Xinyuan-LilyGO/T-Embed/examples/factory/src/knob.png

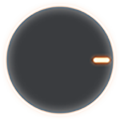
examples/factory/src/knob.png
