Xinyuan-LilyGO/T-Embed/image/front-panel.jpg

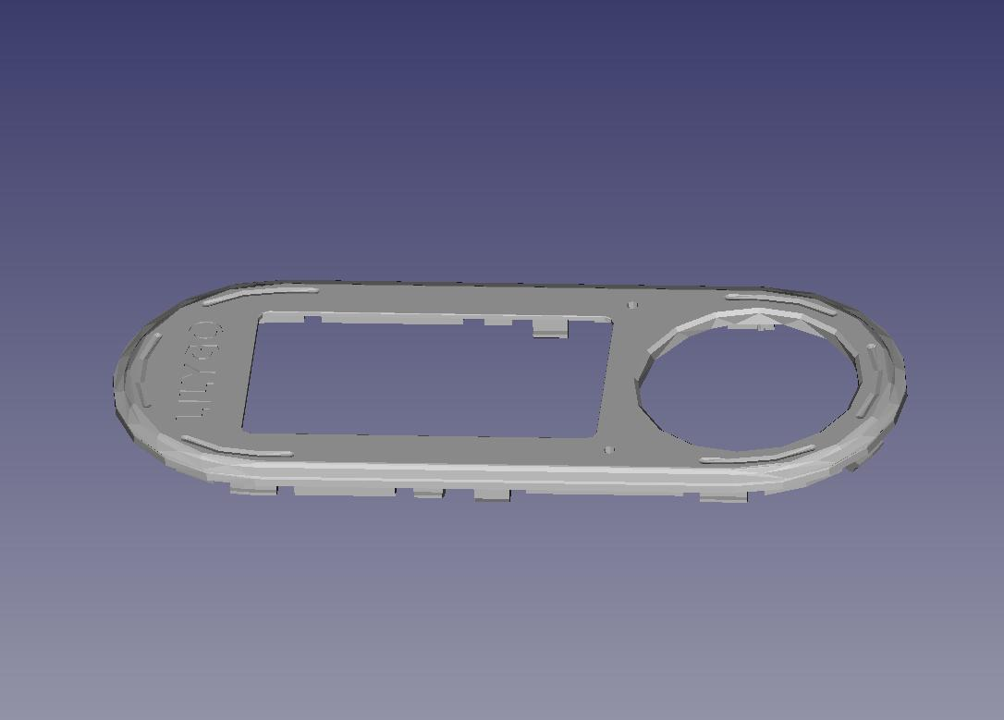
image/front-panel.jpg
