Xinyuan-LilyGO/T-Embed/examples/CC1101_Receive/CC1101_Receive.ino

/**
 * @file      CC1101_Transmit.ino
 * @author    Lewis He (lewishe@outlook.com)
 * @license   MIT
 * @copyright Copyright (c) 2023  Shenzhen Xin Yuan Electronic Technology Co., Ltd
 * @date      2023-10-19
 * @note      The sketch only works with CC1101 + NFC Shield
 */

#include <RadioLib.h>
#include <Adafruit_PN532.h>
#include "TFTHelper.h"
#include "OneButton.h"

static float freq = 0;

enum CC1101_Freq  {
    FREQ_315MHZ,
    FREQ_434MHZ,
    FREQ_868MHZ,
    FREQ_915MHZ,
};

SPIClass newSPI =  SPIClass(HSPI);
CC1101 radio = new Module(SHIELD_RADIO_CS_PIN,
                          SHIELD_RADIO_DIO0_PIN,
                          SHIELD_RADIO_RST_PIN,
                          -1,
                          newSPI);
Adafruit_PN532 nfc(SHIELD_NFC_CS_PIN, &newSPI);

TFT_eSprite spr = TFT_eSprite(&tft);
TFT_eSprite sprTitle = TFT_eSprite(&tft);
TFT_eSprite nfcSpr = TFT_eSprite(&tft);
OneButton button(BOARD_ENCODE_CENTEN_PIN, true);

int spr_w = 0;
int spr_h = 0;
int spr_start_x = 0;
int spr_start_y = 0;
int start_x ;
int title_h ;
SemaphoreHandle_t radioLock;
uint8_t currFreq = FREQ_868MHZ;
bool nfcOnline = true;

void readMifareClassic(void);

void setFreq( CC1101_Freq f)
{
    switch (f) {
    case FREQ_315MHZ:
        digitalWrite(SHIELD_RADIO_SW1_PIN, HIGH);
        digitalWrite(SHIELD_RADIO_SW0_PIN, LOW);
        freq = 315.0;
        return;
    case FREQ_434MHZ:
        digitalWrite(SHIELD_RADIO_SW1_PIN, HIGH);
        digitalWrite(SHIELD_RADIO_SW0_PIN, HIGH);
        freq = 434.0;
        return;
    case FREQ_868MHZ:
        freq = 868.0;
        digitalWrite(SHIELD_RADIO_SW1_PIN, LOW);
        digitalWrite(SHIELD_RADIO_SW0_PIN, HIGH);
        return;
    case FREQ_915MHZ:
        freq = 915.0;
        digitalWrite(SHIELD_RADIO_SW1_PIN, LOW);
        digitalWrite(SHIELD_RADIO_SW0_PIN, HIGH);
        return;
    default:
        break;
    }
    freq = 868.0;
    digitalWrite(SHIELD_RADIO_SW1_PIN, LOW);
    digitalWrite(SHIELD_RADIO_SW0_PIN, HIGH);
}


void clickCallback()
{
    Serial.println("Cilick");
    currFreq++;
    currFreq %= (FREQ_915MHZ + 1);
    setFreq((CC1101_Freq)currFreq);
    if (xSemaphoreTake(radioLock, portMAX_DELAY)) {
        // set carrier frequency
        if (radio.setFrequency(freq) == RADIOLIB_ERR_INVALID_FREQUENCY) {
            Serial.println(F("[CC1101] Selected frequency is invalid for this module!"));
            tft.println(F("[CC1101] Selected frequency is invalid for this module!"));
        } else {
            Serial.println(F("[CC1101] Selected frequency successed!"));
        }

        String str = String(freq);
        str.concat("MHz");

        sprTitle.setFreeFont(&FreeMono9pt7b);
        sprTitle.drawString("Recvive:", 15, 5);
        sprTitle.drawString(str, 15, 25);
        sprTitle.pushSprite(0, 0);

        xSemaphoreGive(radioLock);
    }
}


void buttonLoop(void *)
{
    while (1) {
        button.tick();
        delay(5);
    }
}

void setup()
{
    Serial.begin(115200);

    // Create lock
    radioLock = xSemaphoreCreateBinary();
    xSemaphoreGive(radioLock);

    // Using battery requires setting IO46 to HIGH,
    // otherwise the device will not allow
    pinMode(BOARD_POWER_ON_PIN, OUTPUT);
    digitalWrite(BOARD_POWER_ON_PIN, HIGH);

    // Initialize display screen
    initTFT();

    spr_w = tft.width();
    spr_h = tft.width() / 3;

    // Radio and NFC ,SD share the SPI bus.
    // Before using it, turn off and disable all devices
    // on the same bus.
    pinMode(SHIELD_RADIO_CS_PIN, OUTPUT);
    digitalWrite(SHIELD_RADIO_CS_PIN, HIGH);

    pinMode(SHIELD_NFC_CS_PIN, OUTPUT);
    digitalWrite(SHIELD_NFC_CS_PIN, HIGH);

    pinMode(BOARD_SDCARD_CS_PIN, OUTPUT);
    digitalWrite(BOARD_SDCARD_CS_PIN, HIGH);

    //Set antenna frequency settings
    pinMode(SHIELD_RADIO_SW1_PIN, OUTPUT);
    pinMode(SHIELD_RADIO_SW0_PIN, OUTPUT);
    //Set CC1101 frequency
    setFreq(FREQ_868MHZ);

    // Initialize SPI
    newSPI.begin(BOARD_SPI_SCK_PIN, BOARD_SPI_MISO_PIN, BOARD_SPI_MOSI_PIN);


    nfc.begin();
    uint32_t versiondata = nfc.getFirmwareVersion();
    if (! versiondata) {
        Serial.println("Didn't find PN53x chip");
        tft.println("Didn't find PN53x chip");
        delay(1000);
        nfcOnline = false;
    } else {
        // Got ok data, print it out!
        Serial.print("Found chip PN5"); Serial.println((versiondata >> 24) & 0xFF, HEX);
        Serial.print("Firmware ver. "); Serial.print((versiondata >> 16) & 0xFF, DEC);
        Serial.print('.'); Serial.println((versiondata >> 8) & 0xFF, DEC);
        Serial.println("Waiting for an ISO14443A Card ...");
    }


    // initialize CC1101
    Serial.print(F("[CC1101] Initializing ... "));
    Serial.print(freq);
    Serial.print(" MHz ");

    tft.print(F("[CC1101] Initializing ... "));
    tft.print(freq);
    tft.print(" MHz ");

    int state = radio.begin(freq);
    if (state == RADIOLIB_ERR_NONE) {
        Serial.println(F("success!"));
        tft.println(F("success!"));
    } else {
        Serial.print(F("failed, code "));
        Serial.println(state);
        tft.print(F("failed, code "));
        tft.println(state);
        while (true);
    }


    // you can also change the settings at runtime
    // and check if the configuration was changed successfully

    // set carrier frequency to 433.5 MHz
    if (radio.setFrequency(freq) == RADIOLIB_ERR_INVALID_FREQUENCY) {
        Serial.println(F("[CC1101] Selected frequency is invalid for this module!"));
        tft.println(F("[CC1101] Selected frequency is invalid for this module!"));
        while (true);
    }

    // Too high an air rate may result in data loss
    // Set bit rate to 5 kbps
    state = radio.setBitRate(5);
    if (state == RADIOLIB_ERR_INVALID_BIT_RATE) {
        Serial.println(F("[CC1101] Selected bit rate is invalid for this module!"));
        tft.println(F("[CC1101] Selected bit rate is invalid for this module!"));
        while (true);
    } else if (state == RADIOLIB_ERR_INVALID_BIT_RATE_BW_RATIO) {
        Serial.println(F("[CC1101] Selected bit rate to bandwidth ratio is invalid!"));
        Serial.println(F("[CC1101] Increase receiver bandwidth to set this bit rate."));
        tft.println(F("[CC1101] Increase receiver bandwidth to set this bit rate."));
        while (true);
    }

    // set receiver bandwidth to 135.0 kHz
    if (radio.setRxBandwidth(135.0) == RADIOLIB_ERR_INVALID_RX_BANDWIDTH) {
        Serial.println(F("[CC1101] Selected receiver bandwidth is invalid for this module!"));
        tft.println(F("[CC1101] Selected receiver bandwidth is invalid for this module!"));
        while (true);
    }

    // set allowed frequency deviation to 10.0 kHz
    if (radio.setFrequencyDeviation(10.0) == RADIOLIB_ERR_INVALID_FREQUENCY_DEVIATION) {
        Serial.println(F("[CC1101] Selected frequency deviation is invalid for this module!"));
        tft.println(F("[CC1101] Selected frequency deviation is invalid for this module!"));
        while (true);
    }

    // set output power to 10 dBm
    if (radio.setOutputPower(10) == RADIOLIB_ERR_INVALID_OUTPUT_POWER) {
        Serial.println(F("[CC1101] Selected output power is invalid for this module!"));
        tft.println(F("[CC1101] Selected output power is invalid for this module!"));
        while (true);
    }

    // 2 bytes can be set as sync word
    if (radio.setSyncWord(0x01, 0x23) == RADIOLIB_ERR_INVALID_SYNC_WORD) {
        Serial.println(F("[CC1101] Selected sync word is invalid for this module!"));
        tft.println(F("[CC1101] Selected sync word is invalid for this module!"));
        while (true);
    }

    start_x = (tft.width() / 2) - 2;
    title_h = tft.height() - spr_h - 10;

    sprTitle.createSprite(tft.width() / 2, title_h);
    sprTitle.fillSprite(TFT_BLACK);
    sprTitle.drawRoundRect(0, 0, start_x, title_h, 5, TFT_VIOLET);

    String str = String(freq);
    str.concat("MHz");

    sprTitle.setFreeFont(&FreeMono9pt7b);
    sprTitle.drawString("Recvive:", 15, 5);
    sprTitle.drawString(str, 15, 25);

    sprTitle.pushSprite(0, 0);


    nfcSpr.createSprite(tft.width() / 2, title_h);
    nfcSpr.fillSprite(TFT_BLACK);
    nfcSpr.setFreeFont(&FreeMono9pt7b);
    nfcSpr.drawRoundRect(0, 0, start_x, title_h, 5, TFT_DARKCYAN);
    str = "NFC";
    nfcSpr.drawString(str,  15, 5);
    if (!nfcOnline) {
        nfcSpr.setTextFont(1);
        nfcSpr.setTextColor(TFT_RED);
        str = "FAIL";
        nfcSpr.drawString(str, 15, 25);
    }
    nfcSpr.pushSprite(start_x, 0);


    spr_start_x = 10;
    spr_start_y = 35;
    spr.createSprite(spr_w, spr_h);
    spr.fillSprite(TFT_BLACK);
    spr.drawRoundRect(0, 0, spr_w - 2, spr_h - 2, 5, TFT_ORANGE);
    spr.setCursor(spr_start_x, spr_start_y);
    spr.setFreeFont(&FreeSerif9pt7b);
    spr.println(F("Waiting for incoming transmission ... "));
    spr.pushSprite(0, tft.height() / 3);


    button.attachClick(clickCallback);

    xTaskCreate(buttonLoop, "btn", 2048, NULL, 10, NULL);
}


void loop()
{
    if (nfcOnline) {
        // Block for 2 seconds to read the tag
        readMifareClassic();
    }

    if (xSemaphoreTake(radioLock, pdMS_TO_TICKS(200)) != pdPASS) {
        return;
    }

    Serial.print(F("[CC1101] Waiting for incoming transmission ... "));

    // you can receive data as an Arduino String
    String str;
    int state = radio.receive(str);

    // you can also receive data as byte array
    /*
      byte byteArr[8];
      int state = radio.receive(byteArr, 8);
    */

    if (state == RADIOLIB_ERR_NONE) {

        // Add data filtering to only match the corresponding character prefix.
        // If you do not add a data prefix, it may be interfered by other products with the same frequency.
        if (!str.startsWith("Embed:")) {
            xSemaphoreGive(radioLock);
            return;
        }
        // remove prefix
        str = str.substring(String("Embed:").length());

        // packet was successfully received
        Serial.println(F("success!"));

        // print the data of the packet
        Serial.print(F("[CC1101] Data:\t\t"));
        Serial.println(str);

        // print RSSI (Received Signal Strength Indicator)
        // of the last received packet
        Serial.print(F("[CC1101] RSSI:\t\t"));
        Serial.print(radio.getRSSI());
        Serial.println(F(" dBm"));

        // print LQI (Link Quality Indicator)
        // of the last received packet, lower is better
        Serial.print(F("[CC1101] LQI:\t\t"));
        Serial.println(radio.getLQI());

        spr.fillSprite(TFT_BLACK);
        spr.drawRoundRect(0, 0, spr_w - 2, spr_h - 2, 5, TFT_ORANGE);
        spr.setCursor(spr_start_x, spr_start_y);
        spr.print(F("Data:"));
        spr.println(str);
        // spr.setCursor(spr_start_x, spr_start_y + 15);
        spr.print(F(" \n  RSSI:"));
        spr.print(radio.getRSSI());
        spr.println(F(" dBm"));
        spr.pushSprite(0, tft.height() / 3);

    } else if (state == RADIOLIB_ERR_RX_TIMEOUT) {
        // timeout occurred while waiting for a packet
        Serial.println(F("timeout!"));

    } else if (state == RADIOLIB_ERR_CRC_MISMATCH) {
        // packet was received, but is malformed
        Serial.println(F("CRC error!"));

    } else {
        // some other error occurred
        Serial.print(F("failed, code "));
        Serial.println(state);
    }

    xSemaphoreGive(radioLock);

}

void readMifareClassic(void)
{
    uint8_t success;
    uint8_t uid[] = { 0, 0, 0, 0, 0, 0, 0 };  // Buffer to store the returned UID
    uint8_t uidLength;                        // Length of the UID (4 or 7 bytes depending on ISO14443A card type)

    // Wait for an ISO14443A type cards (Mifare, etc.).  When one is found
    // 'uid' will be populated with the UID, and uidLength will indicate
    // if the uid is 4 bytes (Mifare Classic) or 7 bytes (Mifare Ultralight)
    success = nfc.readPassiveTargetID(PN532_MIFARE_ISO14443A, uid, &uidLength, 2000);
    Serial.print("readPassiveTargetID:");
    Serial.println(success);
    if (success) {
        // Display some basic information about the card
        Serial.println("Found an ISO14443A card");
        Serial.print("  UID Length: "); Serial.print(uidLength, DEC); Serial.println(" bytes");
        Serial.print("  UID Value: ");
        nfc.PrintHex(uid, uidLength);


        //Show uid
        nfcSpr.fillSprite(TFT_BLACK);
        nfcSpr.drawRoundRect( 2, 0, start_x, title_h, 5, TFT_DARKCYAN);
        nfcSpr.setFreeFont(&FreeMono9pt7b);

        String str = "NFC";
        nfcSpr.drawString(str,  15, 5);
        nfcSpr.setTextFont(1);
        str = "UID:";
        str.concat(uid[0]); str.concat(':');
        str.concat(uid[1]); str.concat(':');
        str.concat(uid[2]); str.concat(':');
        str.concat(uid[3]);
        nfcSpr.drawString(str, 15, 25);

        nfcSpr.pushSprite(start_x, 0);

        if (uidLength == 4) {
            // We probably have a Mifare Classic card ...
            uint32_t cardid = uid[0];
            cardid <<= 8;
            cardid |= uid[1];
            cardid <<= 8;
            cardid |= uid[2];
            cardid <<= 8;
            cardid |= uid[3];
            Serial.print("Seems to be a Mifare Classic card #");
            Serial.println(cardid);
        }
        Serial.println("");
    } else {
        nfcSpr.fillSprite(TFT_BLACK);
        String str = "NFC";
        nfcSpr.setFreeFont(&FreeMono9pt7b);
        nfcSpr.drawRoundRect( 2, 0, start_x, title_h, 5, TFT_DARKCYAN);
        nfcSpr.drawString(str,  15, 5);
        nfcSpr.pushSprite(start_x, 0);
    }
}
