Xinyuan-LilyGO/T-Embed/examples/factory/src/img_controller.c

#if defined(LV_CONF_INCLUDE_SIMPLE)
#include "lvgl.h"
#else
 #include "lvgl.h"
#endif


#ifndef LV_ATTRIBUTE_MEM_ALIGN
#define LV_ATTRIBUTE_MEM_ALIGN
#endif

#ifndef LV_ATTRIBUTE_IMG_IMG_CONTROLLER
#define LV_ATTRIBUTE_IMG_IMG_CONTROLLER
#endif

const LV_ATTRIBUTE_MEM_ALIGN LV_ATTRIBUTE_LARGE_CONST LV_ATTRIBUTE_IMG_IMG_CONTROLLER uint8_t img_controller_map[] = {
#if LV_COLOR_DEPTH == 1 || LV_COLOR_DEPTH == 8
  /*Pixel format: Alpha 8 bit, Red: 3 bit, Green: 3 bit, Blue: 2 bit*/
  0x00, 0x00, 0x00, 0x00, 0x00, 0x00, 0x00, 0x00, 0x00, 0x00, 0x00, 0x00, 0x00, 0x00, 0x00, 0x8d, 0x00, 0xe8, 0x00, 0xf2, 0x00, 0xf2, 0x00, 0xf2, 0x00, 0xf2, 0x00, 0xf2, 0x00, 0xf2, 0x00, 0xf2, 0x00, 0xf2, 0x00, 0xf2, 0x00, 0xf2, 0x00, 0xc1, 0x00, 0x29, 0x00, 0x00, 0x00, 0x00, 0x00, 0x00, 0x00, 0x00, 0x00, 0x00, 0x00, 0x00, 0x00, 0x00, 0x00, 0x00, 0x00, 0x00, 0x00, 0x00, 0x00, 0x00, 0x00, 0x00, 0x00, 0x51, 0x00, 0xd3, 0x00, 0xf2, 0x00, 0xf2, 0x00, 0xf2, 0x00, 0xf2, 0x00, 0xf2, 0x00, 0xf2, 0x00, 0xf2, 0x00, 0xf2, 0x00, 0xf2, 0x00, 0xf2, 0x00, 0xde, 0x00, 0x69, 0x00, 0x00, 0x00, 0x00, 0x00, 0x00, 0x00, 0x00, 0x00, 0x00, 0x00, 0x00, 0x00, 0x00, 0x00, 0x00, 0x00, 0x00, 0x00, 0x00, 0x00, 0x00, 0x00, 0x00, 0x00, 0x17, 0x00, 0xb5, 0x00, 0xf2, 0x00, 0xf2, 0x00, 0xf2, 0x00, 0xf2, 0x00, 0xf2, 0x00, 0xf2, 0x00, 0xf2, 0x00, 0xf2, 0x00, 0xf2, 0x00, 0xf2, 0x00, 0xee, 0x00, 0x9f, 0x00, 0x09, 0x00, 0x00, 0x00, 0x00, 0x00, 0x00, 0x00, 0x00, 0x00, 0x00, 0x00, 0x00, 
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
