Xinyuan-LilyGO/T-Embed/examples/factory/src/alibaba_font.c

/*******************************************************************************
 * Size: 40 px
 * Bpp: 4
 * Opts: 
 ******************************************************************************/

#ifdef LV_CONF_INCLUDE_SIMPLE
#include "lvgl.h"
#else
 #include "lvgl.h"
#endif

#ifndef ALIBABA_FONT
#define ALIBABA_FONT 1
#endif

#if ALIBABA_FONT

/*-----------------
 *    BITMAPS
 *----------------*/

/*Store the image of the glyphs*/
static LV_ATTRIBUTE_LARGE_CONST const uint8_t glyph_bitmap[] = {
    /* U+0020 " " */

    /* U+0021 "!" */
    0x7f, 0xff, 0xff, 0xff, 0xc6, 0xff, 0xff, 0xff,
    0xfb, 0x6f, 0xff, 0xff, 0xff, 0xa5, 0xff, 0xff,
    0xff, 0xf9, 0x4f, 0xff, 0xff, 0xff, 0x83, 0xff,
    0xff, 0xff, 0xf7, 0x2f, 0xff, 0xff, 0xff, 0x61,
    0xff, 0xff, 0xff, 0xf5, 0xf, 0xff, 0xff, 0xff,
    0x40, 0xff, 0xff, 0xff, 0xf4, 0xe, 0xff, 0xff,
    0xff, 0x30, 0xdf, 0xff, 0xff, 0xf2, 0xc, 0xff,
    0xff, 0xff, 0x10, 0xcf, 0xff, 0xff, 0xf0, 0xb,
    0xff, 0xff, 0xff, 0x0, 0xaf, 0xff, 0xff, 0xe0,
    0x1, 0x33, 0x33, 0x32, 0x0, 0x0, 0x0, 0x0,
    0x0, 0x0, 0x0, 0x0, 0x0, 0x0, 0x0, 0x0,
    0x0, 0x0, 0x5, 0xbd, 0xee, 0xc7, 0x1, 0xff,
    0xff, 0xff, 0xf6, 0x5f, 0xff, 0xff, 0xff, 0x96,
    0xff, 0xff, 0xff, 0xfa, 0x6f, 0xff, 0xff, 0xff,
    0xa5, 0xff, 0xff, 0xff, 0xf9, 0x2f, 0xff, 0xff,
    0xff, 0x60, 0x6d, 0xff, 0xfe, 0x90,

    /* U+0022 "\"" */
    0x2d, 0xdd, 0xdd, 0xd8, 0x9, 0xdd, 0xdd, 0xdd,
    0x21, 0xff, 0xff, 0xff, 0x80, 0xaf, 0xff, 0xff,
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
    0xff, 0xff, 0xff, 0xec, 0xa0, 0x0, 0xb, 0xff,
    0xff, 0xff, 0xff, 0xfd, 0x0, 0x0, 0x7f, 0xff,
    0xff, 0xff, 0xff, 0xd0, 0x0, 0x1, 0xef, 0xff,
    0xff, 0xff, 0xfd, 0x0, 0x0, 0x3, 0xef, 0xff,
    0xff, 0xff, 0xd0, 0x0, 0x0, 0x1, 0x6b, 0xdf,
    0xff, 0xfb, 0x0,
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
